cekim-git/Toolchanger/UserMods/FlisherOfatale/Temporary_Backplate/image1.png

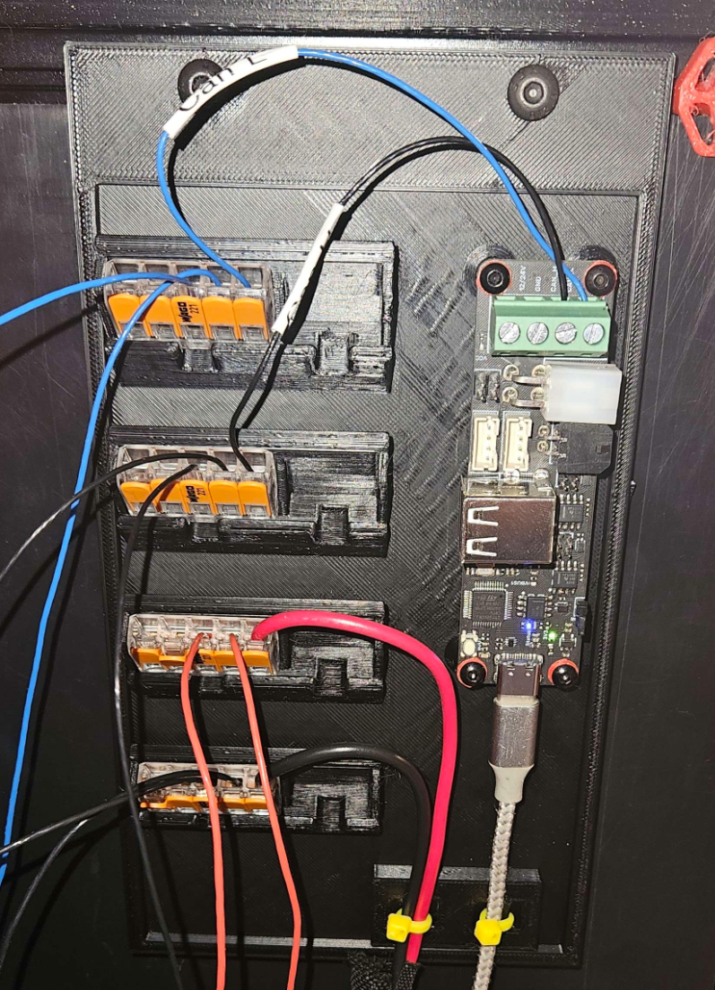
UserMods/FlisherOfatale/Temporary_Backplate/image1.png
